Plouf-0/Domo-Garden/Tests/aerial_node/gpd-switch/autogen/sl_component_catalog.h

#ifndef SL_COMPONENT_CATALOG_H
#define SL_COMPONENT_CATALOG_H

// APIs present in project
#define SL_CATALOG_CLI_PRESENT
#define SL_CATALOG_CLOCK_MANAGER_PRESENT
#define SL_CATALOG_DEVICE_INIT_PRESENT
#define SL_CATALOG_DEVICE_INIT_CORE_PRESENT
#define SL_CATALOG_DEVICE_INIT_DCDC_PRESENT
#define SL_CATALOG_DEVICE_INIT_EMU_PRESENT
#define SL_CATALOG_EMLIB_CORE_PRESENT
#define SL_CATALOG_EMLIB_CORE_DEBUG_CONFIG_PRESENT
#define SL_CATALOG_INTERRUPT_MANAGER_PRESENT
#define SL_CATALOG_IOSTREAM_PRESENT
#define SL_CATALOG_IOSTREAM_EUSART_PRESENT
#define SL_CATALOG_IOSTREAM_UART_COMMON_PRESENT
#define SL_CATALOG_MEMORY_MANAGER_PRESENT
#define SL_CATALOG_NVM3_PRESENT
#define SL_CATALOG_PRINTF_PRESENT
#define SL_CATALOG_RAIL_LIB_PRESENT
#define SL_CATALOG_RAIL_UTIL_INIT_PRESENT
#define SL_CATALOG_RAIL_UTIL_PTI_PRESENT
#define SL_CATALOG_SE_MANAGER_PRESENT
#define SL_CATALOG_BTN0_PRESENT
#define SL_CATALOG_SIMPLE_BUTTON_PRESENT
#define SL_CATALOG_SIMPLE_BUTTON_BTN0_PRESENT
#define SL_CATALOG_LED0_PRESENT
#define SL_CATALOG_SIMPLE_LED_PRESENT
#define SL_CATALOG_SIMPLE_LED_LED0_PRESENT
#define SL_CATALOG_SLEEPTIMER_PRESENT
#define SL_CATALOG_ZIGBEE_DEBUG_PRINT_PRESENT
#define SL_CATALOG_ZIGBEE_GPD_AF_CLI_PRESENT
#define SL_CATALOG_ZIGBEE_GPD_APPLICATION_SUPPORT_PRESENT
#define SL_CATALOG_ZIGBEE_GPD_NETWORK_SUPPORT_PRESENT

#endif // SL_COMPONENT_CATALOG_H
